TinyCircuits/TinyCircuits-TinyShield-GPS-ASD2501/images/ASD2501-R-Tutorial-Image-02.jpg

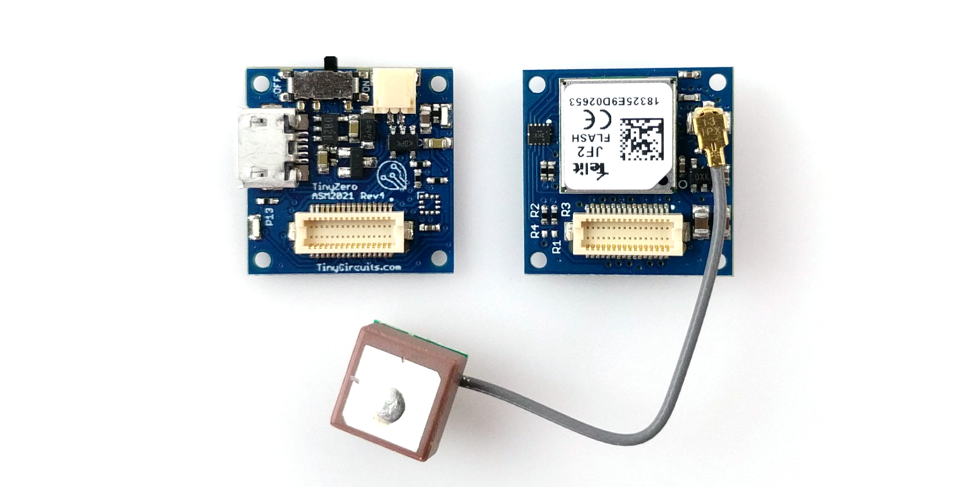
images/ASD2501-R-Tutorial-Image-02.jpg
