TinyCircuits/TinyCircuits-TinyShield-GPS-ASD2501/images/ASD2501-Tutorial-Image-04.png

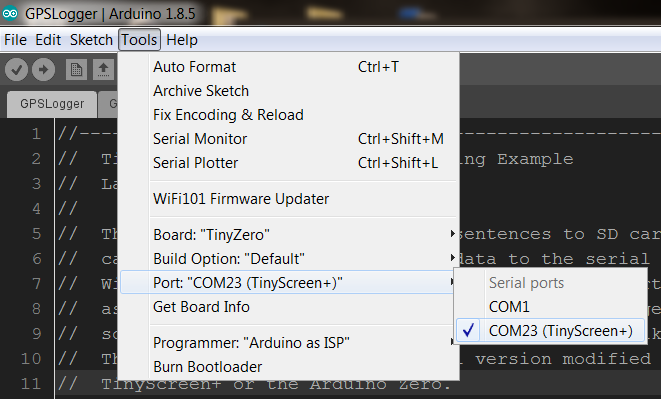
images/ASD2501-Tutorial-Image-04.png
