TinyCircuits/TinyCircuits-TinyShield-GPS-ASD2501/examples/TinyGPS/examples/test_with_gps_device/test_with_gps_device.ino

/* This sample code demonstrates the normal use of a TinyGPS object,
 * customised for the TinyCircuits GPS module.
*/


#include <TinyGPS.h>
#include "GPS.h"

TinyGPS gps;
char buf[32];

#if defined (ARDUINO_ARCH_AVR)
#define SerialMonitorInterface Serial
#include <SoftwareSerial.h>
#elif defined(ARDUINO_ARCH_SAMD)
#define SerialMonitorInterface SerialUSB
#include "SoftwareSerialZero.h"
#endif

// The GPS connection is attached with a software serial port
SoftwareSerial ss(GPS_RXPin, GPS_TXPin);

static void smartdelay(unsigned long ms);
static void print_float(float val, float invalid, int len, int prec);
static void print_int(unsigned long val, unsigned long invalid, int len);
static void print_date(TinyGPS &gps);
static void print_str(const char *str, int len);

void setup()
{
  SerialMonitorInterface.begin(115200);
  ss.begin(GPSBaud);
  while (!SerialMonitorInterface && millis() < 5000); //On TinyScreen+/SAMD21 platform, this will wait until the Serial Monitor is opened or until 5 seconds has passed
  
  SerialMonitorInterface.print("Testing TinyGPS library v. "); SerialMonitorInterface.println(TinyGPS::library_version());
  SerialMonitorInterface.println("by Mikal Hart");
  SerialMonitorInterface.println();
  SerialMonitorInterface.println("Sats HDOP Latitude  Longitude  Fix  Date       Time     Date Alt    Course Speed Card  Distance Course Card  Chars Sentences Checksum");
  SerialMonitorInterface.println("          (deg)     (deg)      Age                      Age  (m)    --- from GPS ----  ---- to London  ----  RX    RX        Fail");
  SerialMonitorInterface.println("-------------------------------------------------------------------------------------------------------------------------------------");
  
  gpsInitPins();
  delay(100);
  SerialMonitorInterface.print("Attempting to wake GPS module.. ");
  gpsOn();
  SerialMonitorInterface.println("done.");
  delay(100);
  while (ss.available())ss.read();
}

void loop()
{
  float flat, flon;
  unsigned long age, date, time, chars = 0;
  unsigned short sentences = 0, failed = 0;
  static const double LONDON_LAT = 51.508131, LONDON_LON = -0.128002;
  
  print_int(gps.satellites(), TinyGPS::GPS_INVALID_SATELLITES, 5);
  print_int(gps.hdop(), TinyGPS::GPS_INVALID_HDOP, 5);
  gps.f_get_position(&flat, &flon, &age);
  print_float(flat, TinyGPS::GPS_INVALID_F_ANGLE, 10, 6);
  print_float(flon, TinyGPS::GPS_INVALID_F_ANGLE, 11, 6);
  print_int(age, TinyGPS::GPS_INVALID_AGE, 5);
  print_date(gps);
  print_float(gps.f_altitude(), TinyGPS::GPS_INVALID_F_ALTITUDE, 7, 2);
  print_float(gps.f_course(), TinyGPS::GPS_INVALID_F_ANGLE, 7, 2);
  print_float(gps.f_speed_kmph(), TinyGPS::GPS_INVALID_F_SPEED, 6, 2);
  print_str(gps.f_course() == TinyGPS::GPS_INVALID_F_ANGLE ? "*** " : TinyGPS::cardinal(gps.f_course()), 6);
  print_int(flat == TinyGPS::GPS_INVALID_F_ANGLE ? 0xFFFFFFFF : (unsigned long)TinyGPS::distance_between(flat, flon, LONDON_LAT, LONDON_LON) / 1000, 0xFFFFFFFF, 9);
  print_float(flat == TinyGPS::GPS_INVALID_F_ANGLE ? TinyGPS::GPS_INVALID_F_ANGLE : TinyGPS::course_to(flat, flon, LONDON_LAT, LONDON_LON), TinyGPS::GPS_INVALID_F_ANGLE, 7, 2);
  print_str(flat == TinyGPS::GPS_INVALID_F_ANGLE ? "*** " : TinyGPS::cardinal(TinyGPS::course_to(flat, flon, LONDON_LAT, LONDON_LON)), 6);

  gps.stats(&chars, &sentences, &failed);
  print_int(chars, 0xFFFFFFFF, 6);
  print_int(sentences, 0xFFFFFFFF, 10);
  print_int(failed, 0xFFFFFFFF, 9);
  SerialMonitorInterface.println();
  
  smartdelay(1000);
}

static void smartdelay(unsigned long ms)
{
  unsigned long start = millis();
  do 
  {
    while (ss.available())
      gps.encode(ss.read());
  } while (millis() - start < ms);
}

static void print_float(float val, float invalid, int len, int prec)
{
  if (val == invalid)
  {
    while (len-- > 1)
      SerialMonitorInterface.print('*');
    SerialMonitorInterface.print(' ');
  }
  else
  {
    SerialMonitorInterface.print(val, prec);
    int vi = abs((int)val);
    int flen = prec + (val < 0.0 ? 2 : 1); // . and -
    flen += vi >= 1000 ? 4 : vi >= 100 ? 3 : vi >= 10 ? 2 : 1;
    for (int i=flen; i<len; ++i)
      SerialMonitorInterface.print(' ');
  }
  smartdelay(0);
}

static void print_int(unsigned long val, unsigned long invalid, int len)
{
  char sz[32];
  if (val == invalid)
    strcpy(sz, "*******");
  else
    sprintf(sz, "%ld", val);
  sz[len] = 0;
  for (int i=strlen(sz); i<len; ++i)
    sz[i] = ' ';
  if (len > 0) 
    sz[len-1] = ' ';
  SerialMonitorInterface.print(sz);
  smartdelay(0);
}

static void print_date(TinyGPS &gps)
{
  int year;
  byte month, day, hour, minute, second, hundredths;
  unsigned long age;
  gps.crack_datetime(&year, &month, &day, &hour, &minute, &second, &hundredths, &age);
  if (age == TinyGPS::GPS_INVALID_AGE)
    SerialMonitorInterface.print("********** ******** ");
  else
  {
    char sz[32];
    sprintf(sz, "%02d/%02d/%02d %02d:%02d:%02d ",
        month, day, year, hour, minute, second);
    SerialMonitorInterface.print(sz);
  }
  print_int(age, TinyGPS::GPS_INVALID_AGE, 5);
  smartdelay(0);
}

static void print_str(const char *str, int len)
{
  int slen = strlen(str);
  for (int i=0; i<len; ++i)
    SerialMonitorInterface.print(i<slen ? str[i] : ' ');
  smartdelay(0);
}
